RMIT-BattleBots/battlebots-parts/dave_components/electronics_housings/v1/Switch housing - Part 1.stl

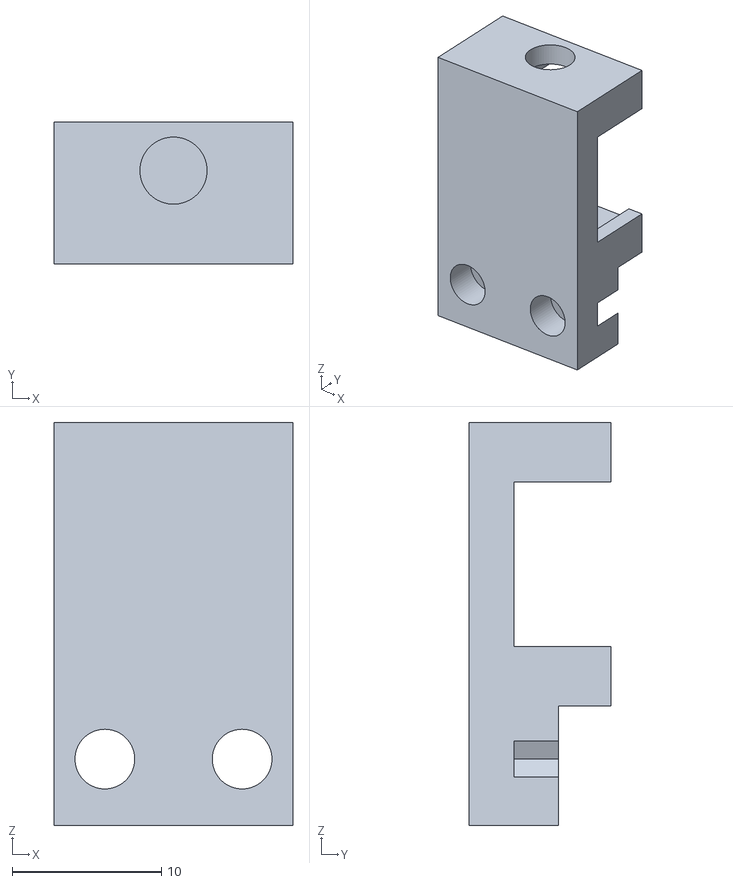
[picture p38: CAD file, 2025-05-16, an earlier design]
dave_components/electronics_housings/v1/Switch housing - Part 1.stl
16.0 x 9.50 x 27.0
