RMIT-BattleBots/battlebots-parts/dave_components/housing/v1/FloorPanel/DaveFloorPanel.STEP

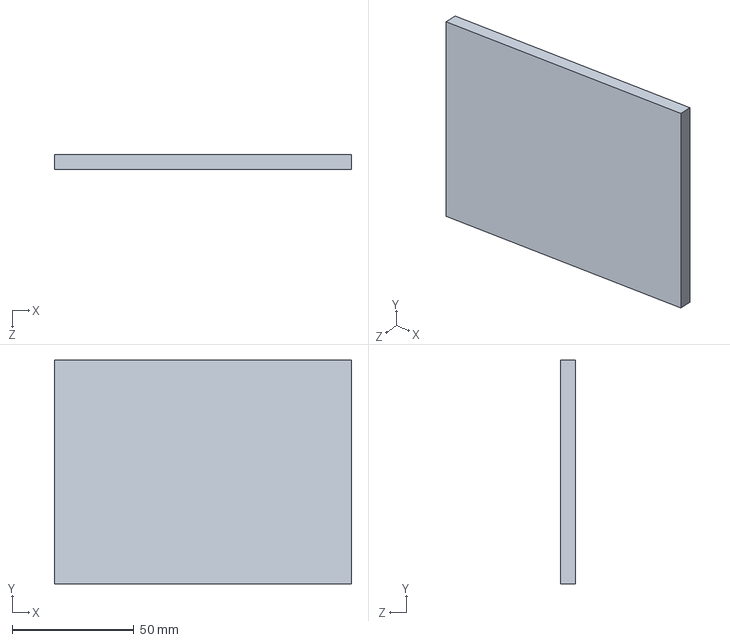
[picture p39: CAD file, 2025-06-26, an earlier design]
dave_components/housing/v1/FloorPanel/DaveFloorPanel.STEP
122.0 x 92.0 x 6.00 mm
