RMIT-BattleBots/battlebots-parts/dave_components/housing/v1/FrontPanel/DaveFrontPanel.STEP

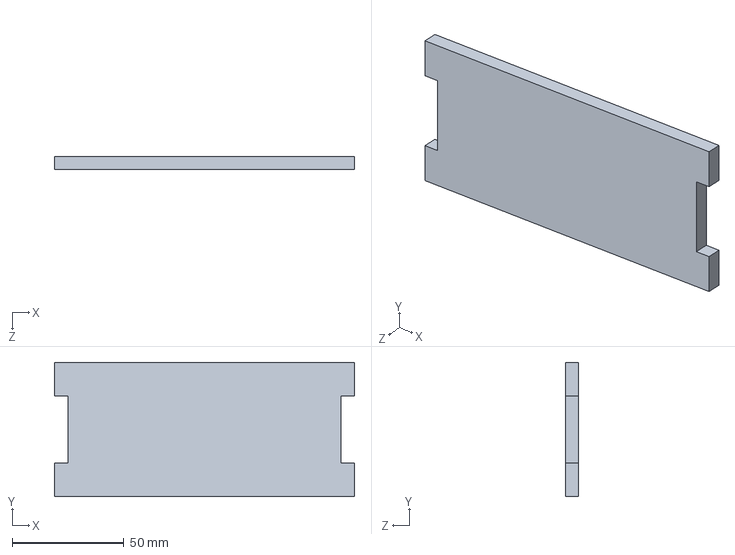
[picture p40: CAD file, 2025-06-26, an earlier design]
dave_components/housing/v1/FrontPanel/DaveFrontPanel.STEP
134.0 x 60.0 x 6.00 mm
