RMIT-BattleBots/battlebots-parts/dave_components/housing/v1/HousingBracket/Bracket BB v3.stl

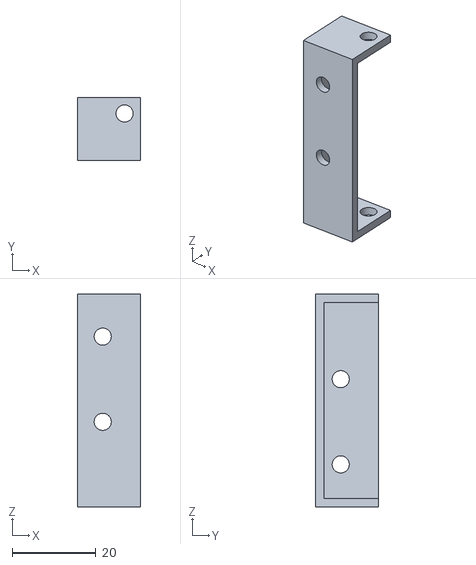
[picture p41: CAD file, 2025-05-16, an earlier design]
dave_components/housing/v1/HousingBracket/Bracket BB v3.stl
15.0 x 15.0 x 51.0
